NickEngmann/8BallGPT/src/Recorder.h

#ifndef RECORDER_H
#define RECORDER_H

#include <Arduino.h>
#include <driver/adc.h>
#include <esp_adc_cal.h>
#include <esp_system.h>
#include <algorithm>

#define ENABLE_DEBUG

// Audio configurations
#define SAMPLE_RATE 32000    
#define CHANNELS 1           // Mono
#define BITS_PER_SAMPLE 16   // Use 16-bit samples in WAV file
#define DC_OFFSET 1250       // 1.25V DC bias from MAX9814
#define SILENCE_TIMEOUT 2000 // Silence detection timeout in ms
#define AUDIO_THRESHOLD 500  // Voice detection sensitivity (adjusted for ADC values)
#define WAV_HEADER_SIZE 44   // Standard WAV header size
#define ENABLE_VOICE_DETECTION // Comment out to disable voice detection

// ADC Configuration
#define ADC_VREF 3300                  // 3.3V reference voltage
#define MAX_RECORD_SECONDS 10          // Maximum recording duration
#define ADC_MIC_CHANNEL ADC1_CHANNEL_1 // GPIO2
#define ADC_MIC_GPIO_NUM 2             // GPIO pin number
#define ADC_MIC_UNIT ADC_UNIT_1        // ADC 1
#define SAMPLE_BUFFER_SIZE 256         // Size of temporary sample buffer
#define DEBUG_INTERVAL 500
#define MAX9814_VPP 2000 // MAX9814 peak-to-peak voltage
// Calculate total buffer size for the entire recording
#define BUFFER_SIZE (MAX_RECORD_SECONDS * SAMPLE_RATE * CHANNELS * 2) // *2 for 16-bit WAV samples

#ifdef ENABLE_DEBUG
#define DEBUG_PRINT(x) Serial.println(x)
#define DEBUG_PRINTF(format, ...) Serial.printf((format), ##__VA_ARGS__)
#else
#define DEBUG_PRINT(x)
#define DEBUG_PRINTF(format, ...)
#endif

// New debug statistics structure
struct DebugStats
{
  uint32_t totalSamples;
  uint32_t missedSamples;
  uint16_t minAmplitude;
  uint16_t maxAmplitude;
  float avgAmplitude;
  uint32_t zeroCrossings;
  unsigned long lastDebugTime;
  size_t lastBufferSize;

  DebugStats() : totalSamples(0),
                 missedSamples(0),
                 minAmplitude(UINT16_MAX),
                 maxAmplitude(0),
                 avgAmplitude(0),
                 zeroCrossings(0),
                 lastDebugTime(0),
                 lastBufferSize(0) {}

  void reset()
  {
    minAmplitude = UINT16_MAX;
    maxAmplitude = 0;
    avgAmplitude = 0;
    zeroCrossings = 0;
  }
};

class VoiceActivatedRecorder
{
public:
  VoiceActivatedRecorder();
  ~VoiceActivatedRecorder();

  bool begin();
  bool startRecording();
  void stopRecording();
  void update();

  uint8_t *getBuffer() { return audioBuffer; }
  size_t getBufferSize() { return bufferIndex; }
  bool isRecording() { return is_recording; }
  float getRecordingProgress();

  // Debug functions
  void printADCInfo();
  void printBufferStatus();
  void printRecordingStatus();
  void debugMicValues(uint16_t *samples, size_t size);

private:
  DebugStats debugStats;
  uint8_t *audioBuffer;          // Main audio buffer
  size_t bufferIndex;            // Current position in buffer
  bool is_recording;             // Recording state
  unsigned long recordStartTime; // When recording started
  unsigned long lastSoundTime;   // Last time voice was detected
  unsigned long lastSampleTime;  // Last time we took a sample
  bool hasDetectedVoice;         // Whether voice has been detected

  // ADC calibration data
  esp_adc_cal_characteristics_t *adc_chars;

  // Memory monitoring
  size_t initialFreeHeap;
  size_t initialFreePSRAM;

  void writeWAVHeader();
  void updateWAVHeader();
  bool detectVoiceActivity(uint16_t *buffer, size_t size);
  void monitorMemory();
  void setupADC();
  int16_t readADCSample();

  // Debug helper functions
  void checkADCSetup();
  void validateBufferSpace();
  void updateDebugStats();
  void printDebugInfo();
};

#endif // RECORDER_H
